Fluffik214/airsoft-battery-module/firmware/src/tusb_config.h

#pragma once
#define CFG_TUSB_MCU            OPT_MCU_STM32F0
#define CFG_TUSB_OS             OPT_OS_NONE
#define CFG_TUSB_DEBUG          0
#define CFG_TUD_ENABLED         1
#define CFG_TUD_MAX_SPEED       OPT_MODE_FULL_SPEED
#define CFG_TUSB_RHPORT0_MODE   (OPT_MODE_DEVICE | OPT_MODE_FULL_SPEED)
#define CFG_TUSB_MEM_SECTION
#define CFG_TUSB_MEM_ALIGN      __attribute__((aligned(4)))
#define CFG_TUD_ENDPOINT0_SIZE  64
#define CFG_TUD_CDC             1
#define CFG_TUD_CDC_RX_BUFSIZE  64
#define CFG_TUD_CDC_TX_BUFSIZE  256
#define CFG_TUD_CDC_EP_BUFSIZE  64
